s-light/LEDBoard_4x4_HD/export/3d/LEDBoard_4x4_HD_rendered.png

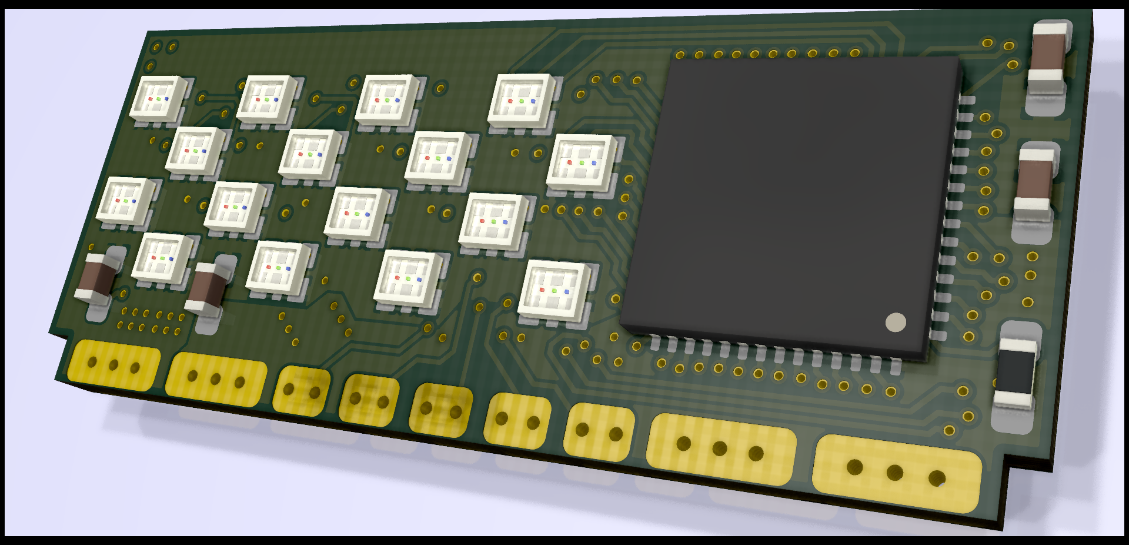
export/3d/LEDBoard_4x4_HD_rendered.png
