s-light/LEDBoard_4x4_HD/export/LEDBoard_4x4_HD-In1.Cu.pdf

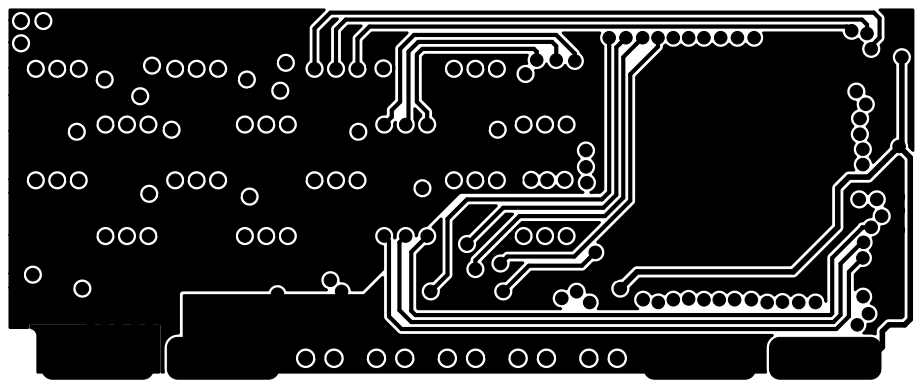
[picture p17: page 1]
