s-light/LEDBoard_4x4_HD/export/LEDBoard_4x4_HD-In2.Cu.pdf

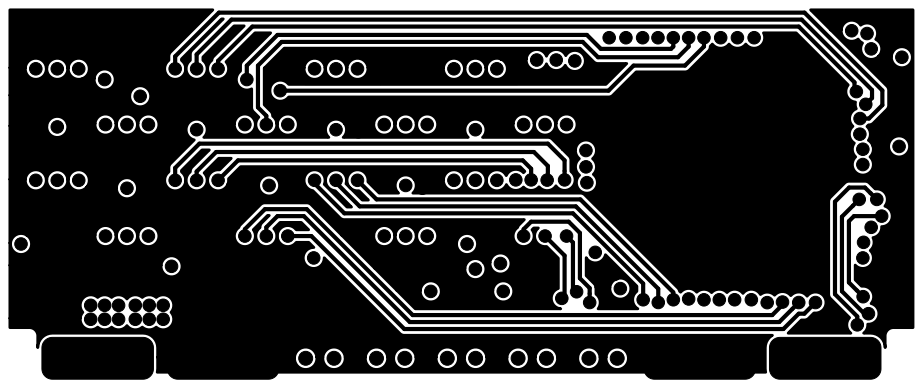
[picture p18: page 1]
